akiratanae/RA4M1_board/board/OUTLINE.pdf

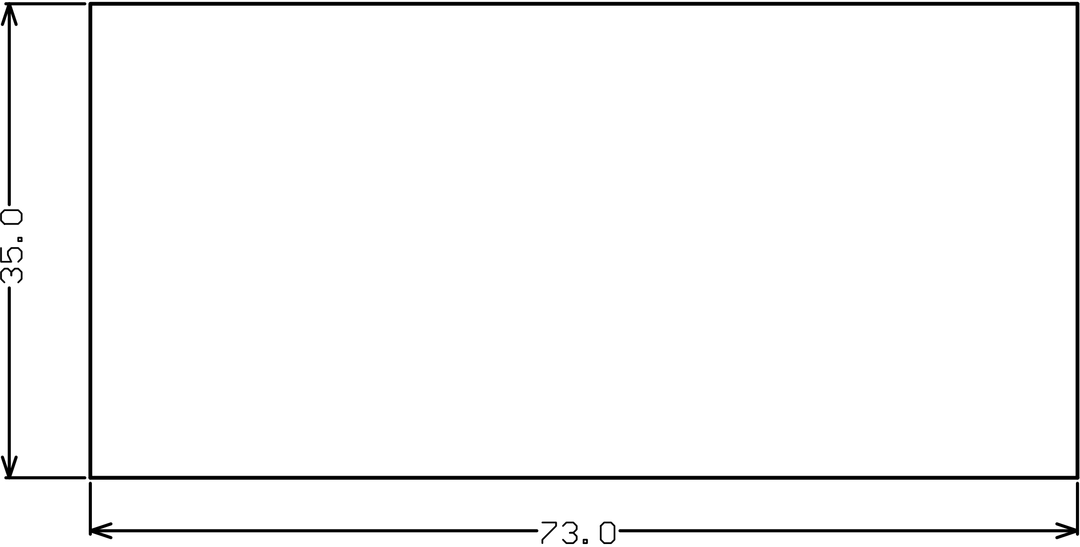
[picture p7: figure]
