akiratanae/RA4M1_board/board/L1_PATTERN.pdf

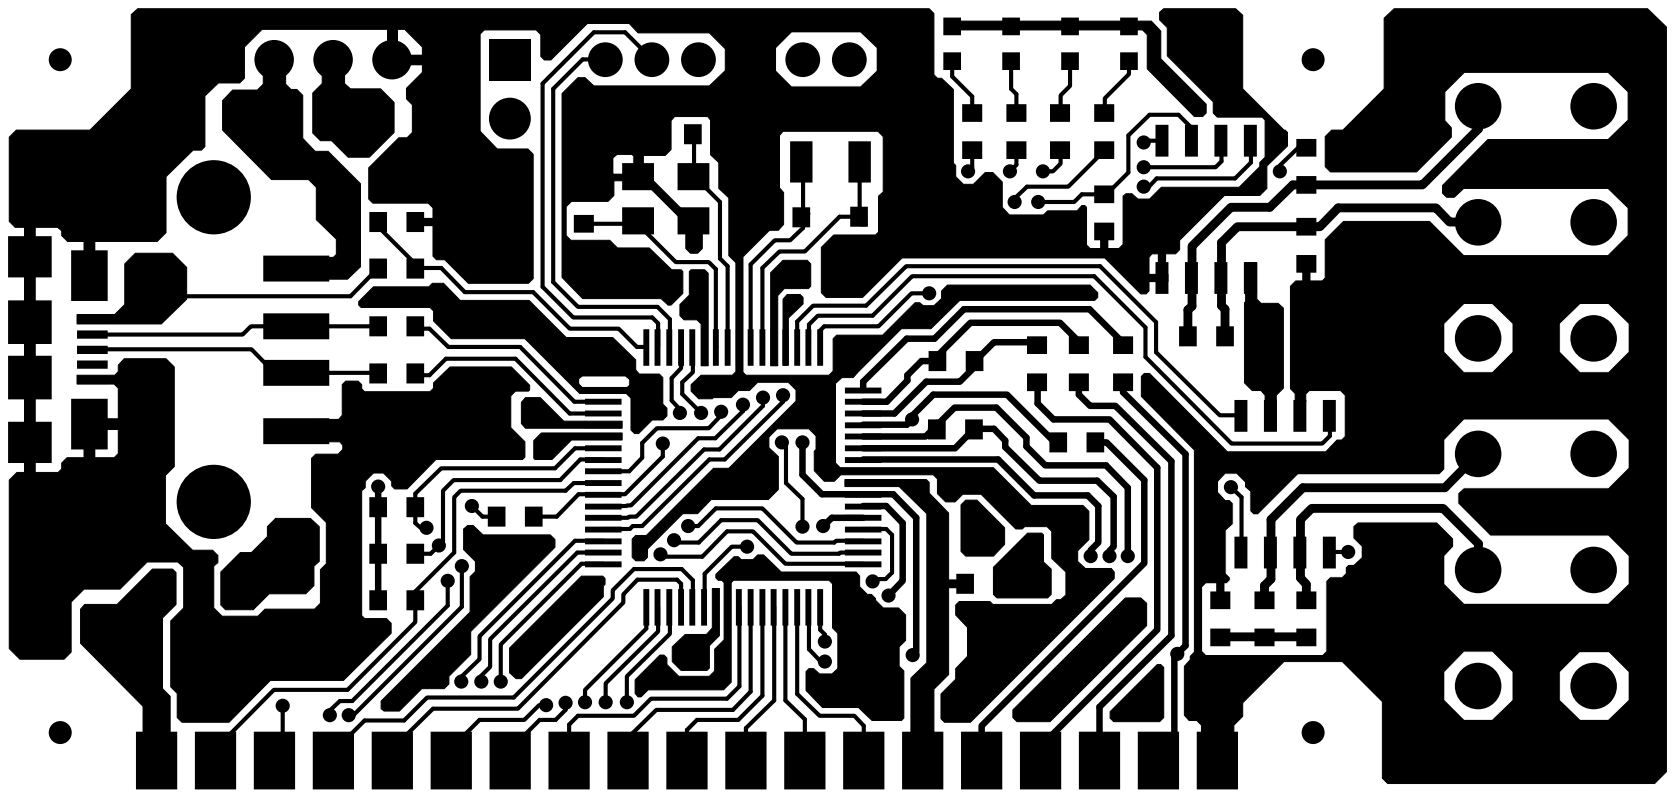
[picture p18: page 1]
