akiratanae/RA4M1_board/board/L1_RESIST.pdf

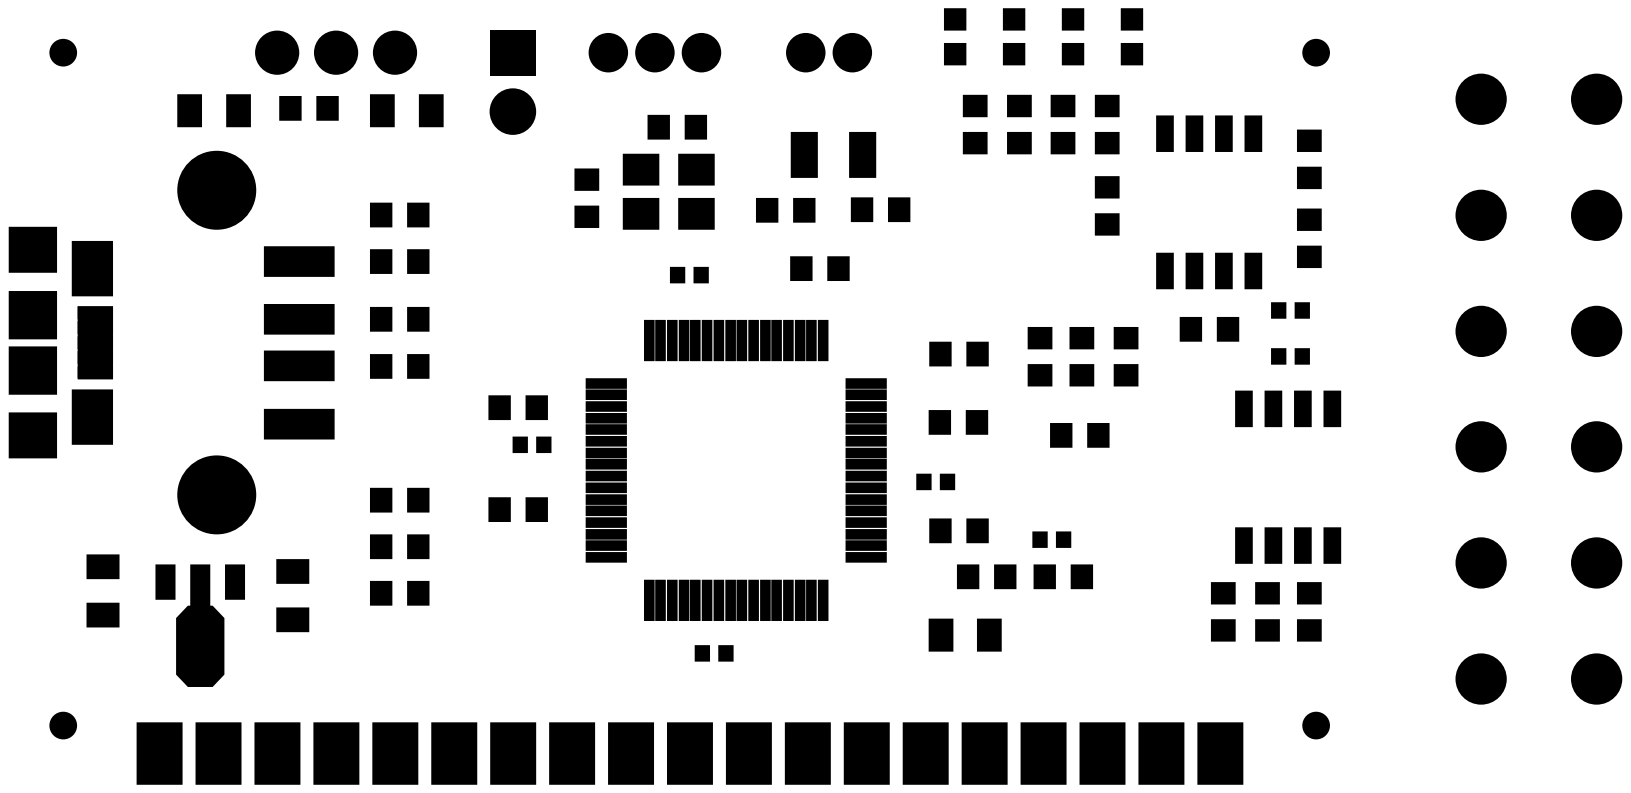
[picture p19: page 1]
