akiratanae/RA4M1_board/board/L1_SILK.pdf

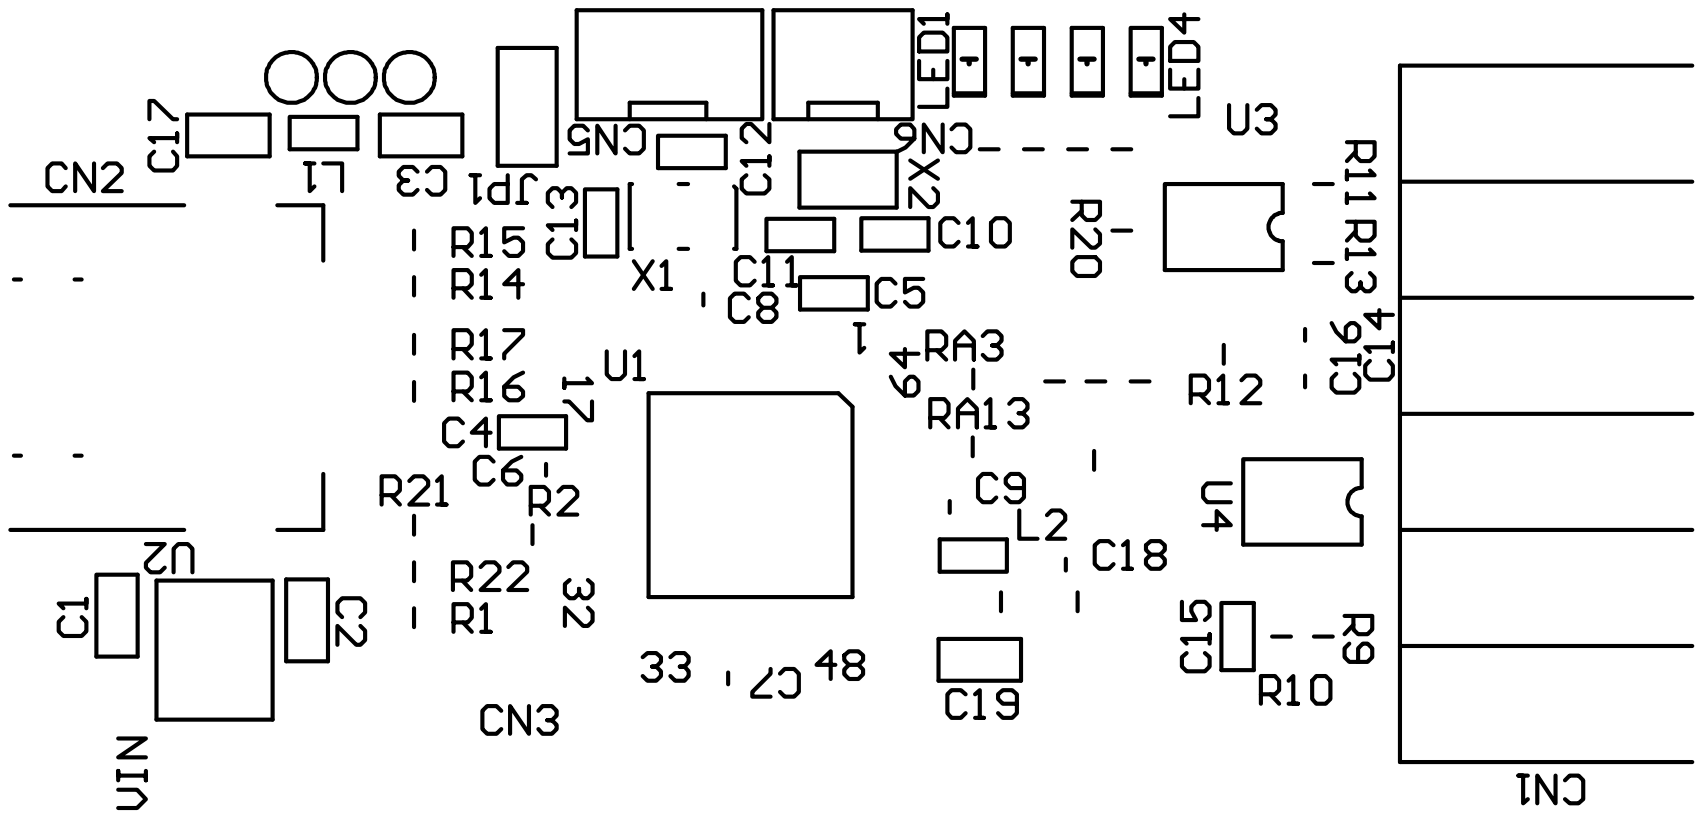
[picture p20: page 1]
