akiratanae/RA4M1_board/board/L2_PATTERN.pdf

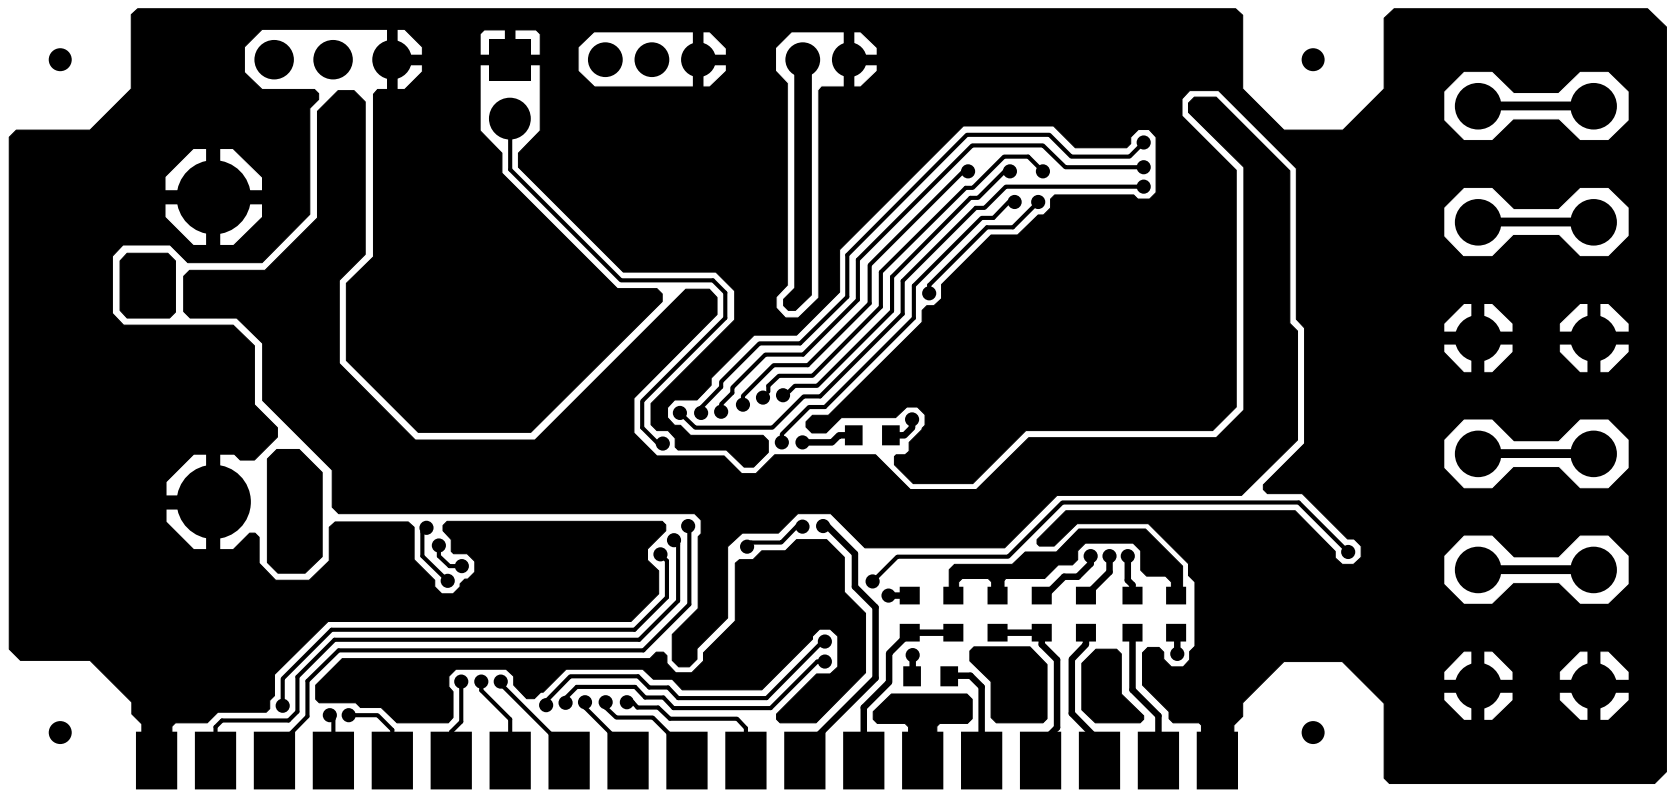
[picture p21: page 1]
